GGChe/Stress-Monitoring-Device/3D modeling Files/keyshot/BOTTOMcase.JPG

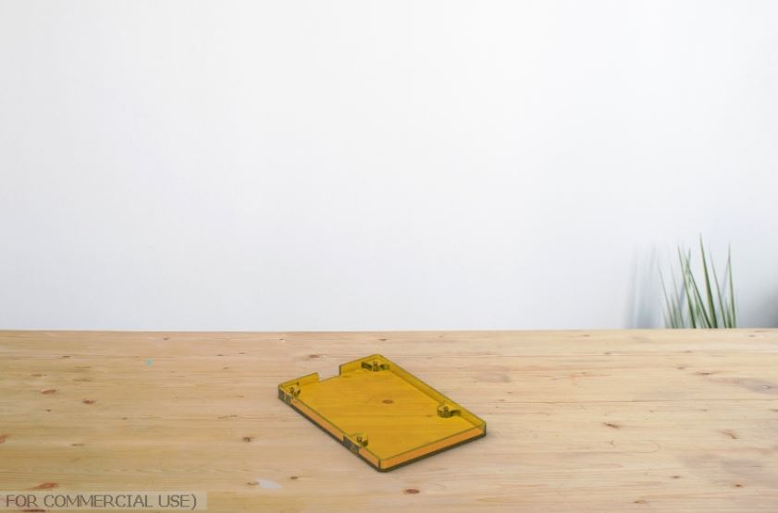
3D modeling Files/keyshot/BOTTOMcase.JPG
