GGChe/Stress-Monitoring-Device/3D modeling Files/keyshot/PCBcase2.jpg

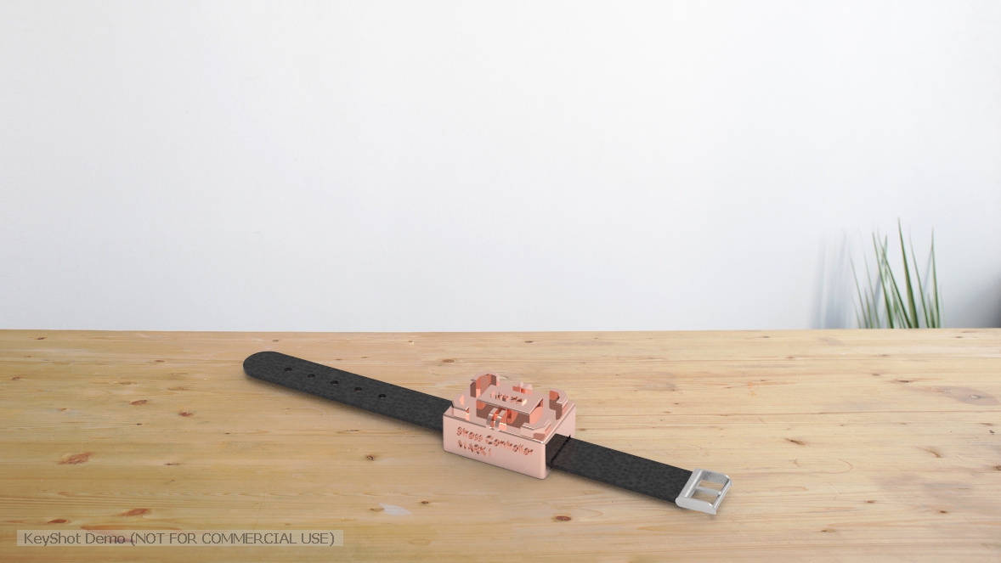
3D modeling Files/keyshot/PCBcase2.jpg
