GGChe/Stress-Monitoring-Device/3D modeling Files/keyshot/Topcase1.jpg

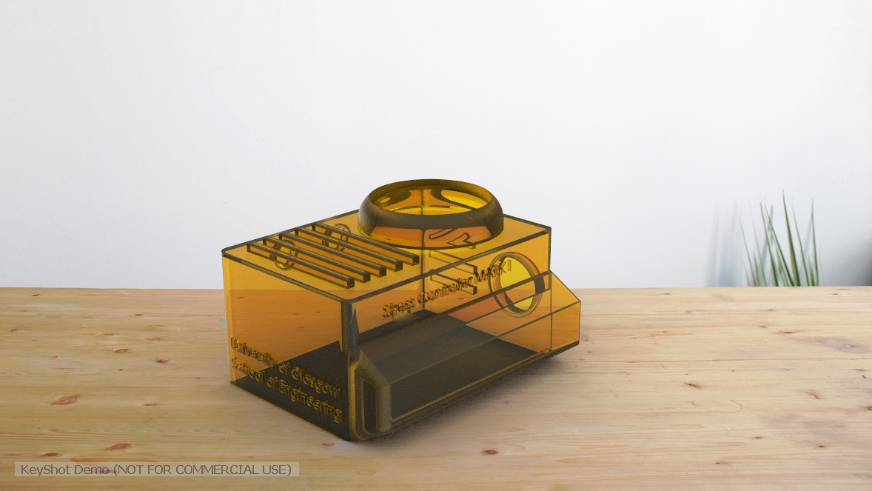
3D modeling Files/keyshot/Topcase1.jpg
