GGChe/Stress-Monitoring-Device/Raspberry Pi Code/code diagram.png

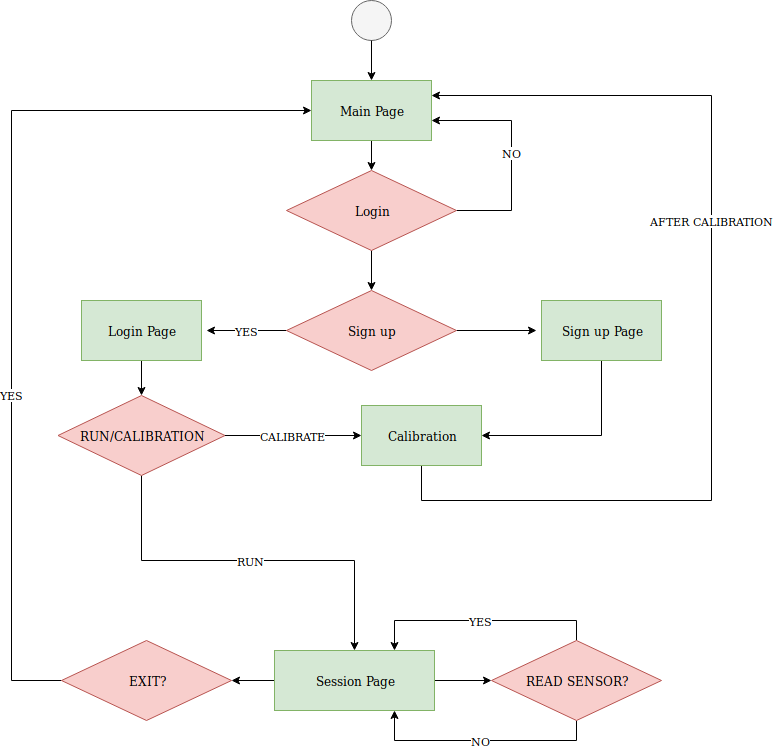
Raspberry Pi Code/code diagram.png
