GGChe/Stress-Monitoring-Device/Webpage/html/mainback.jpg

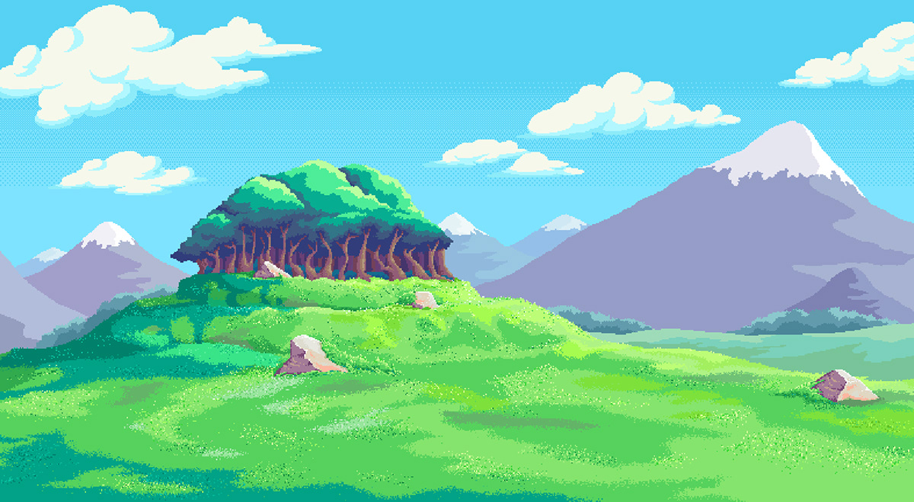
Webpage/html/mainback.jpg
